retsyx/CouchClickerAtomic/other/images/IMG_6382.jpeg

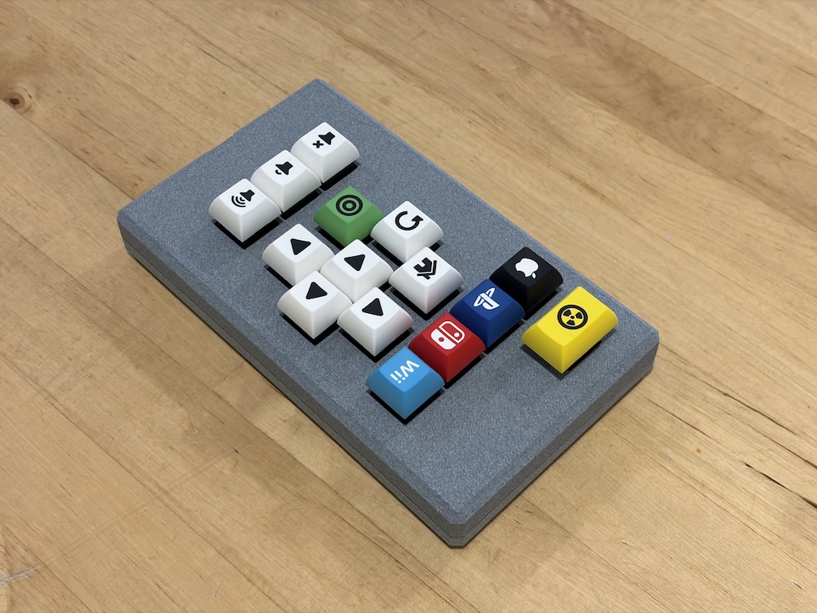
other/images/IMG_6382.jpeg
